JaswantBhartiya/esp32-laser-security/assets/mount_bottom.PNG

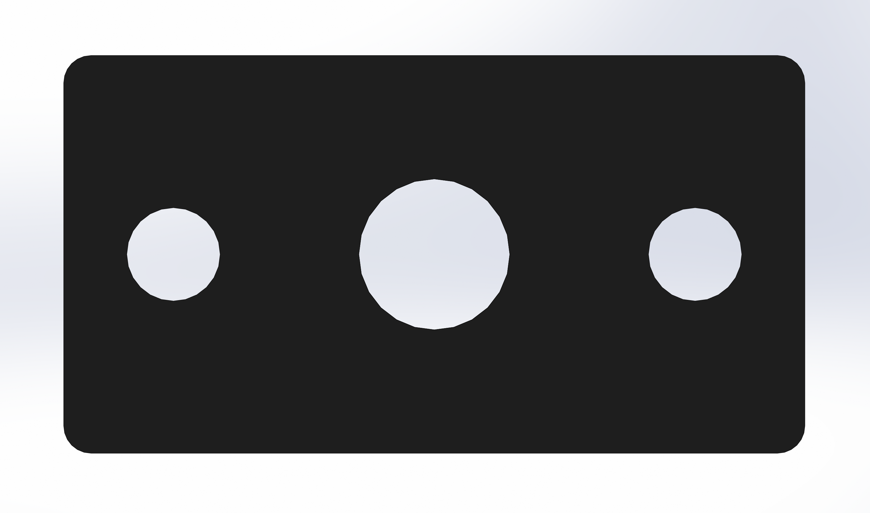
assets/mount_bottom.PNG
