JaswantBhartiya/esp32-laser-security/assets/pcb_raw__isometric.png

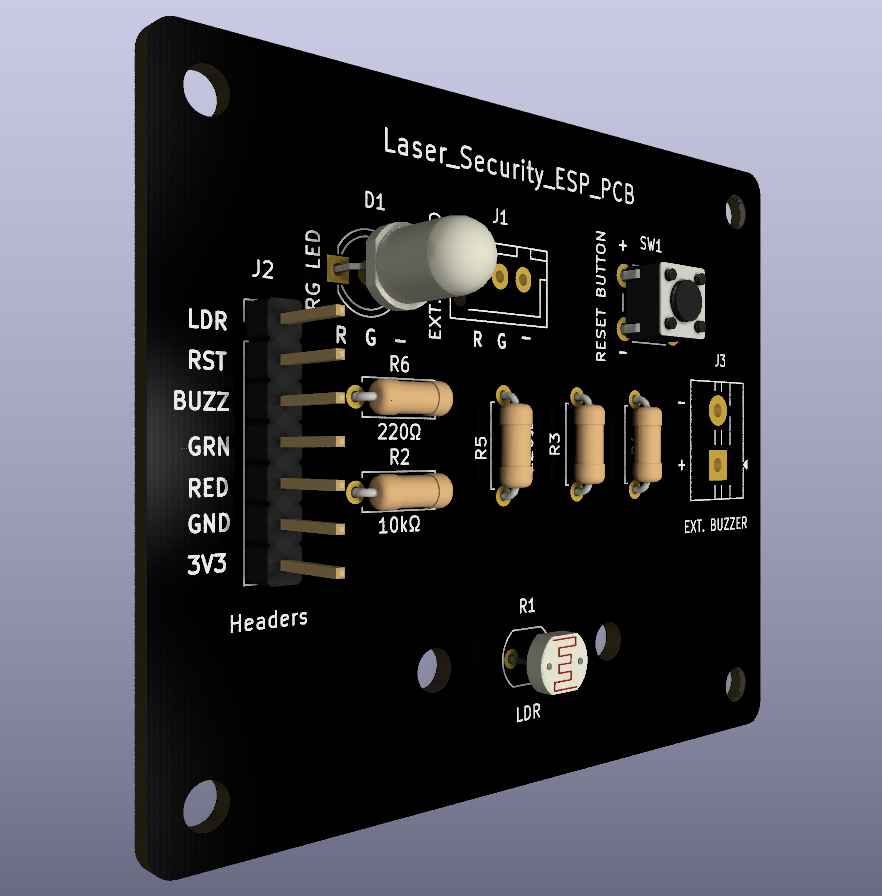
assets/pcb_raw__isometric.png
